Mehdi-KHALFALLAH/My-Arduino-UNO-Design/3D Component Models/3D_Model_ATMEGA16U2-AU.step

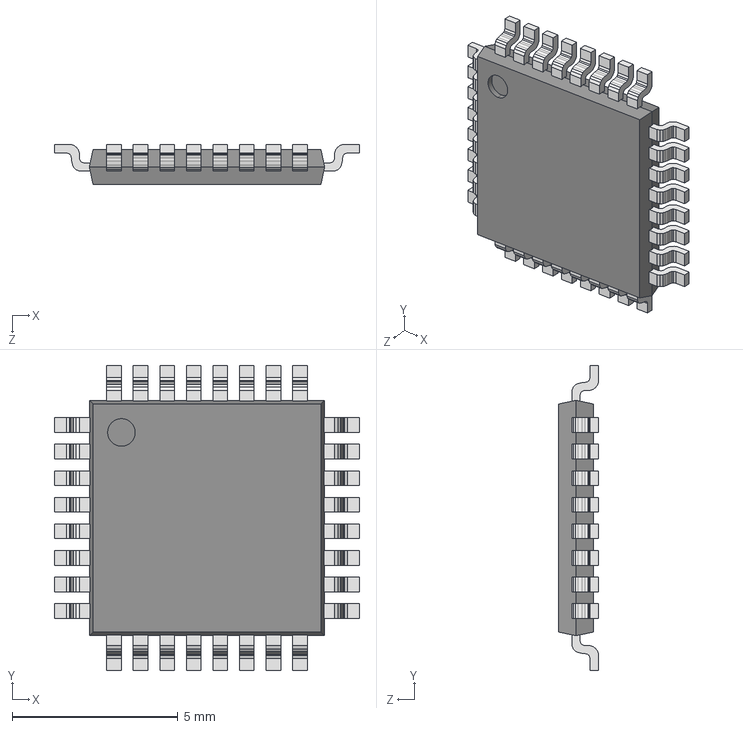
[picture p15: CAD file, 2020-09-16]
3D Component Models/3D_Model_ATMEGA16U2-AU.step
9.20 x 9.20 x 1.20 mm
