Mehdi-KHALFALLAH/My-Arduino-UNO-Design/3D Component Models/dil_socket.stp

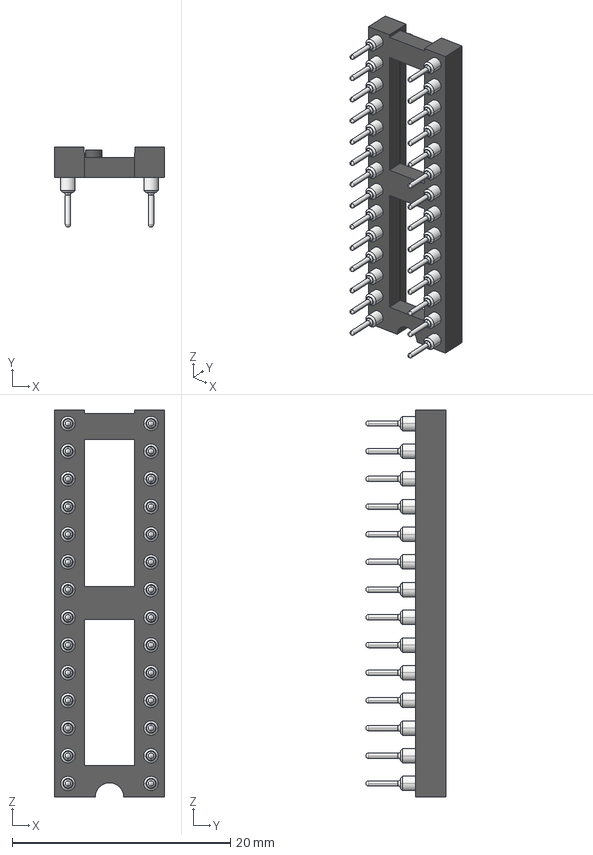
[picture p16: CAD file, 2020-09-16]
3D Component Models/dil_socket.stp
10.1 x 7.37 x 35.5 mm
