Mehdi-KHALFALLAH/My-Arduino-UNO-Design/3D Component Models/capacitor size C.step

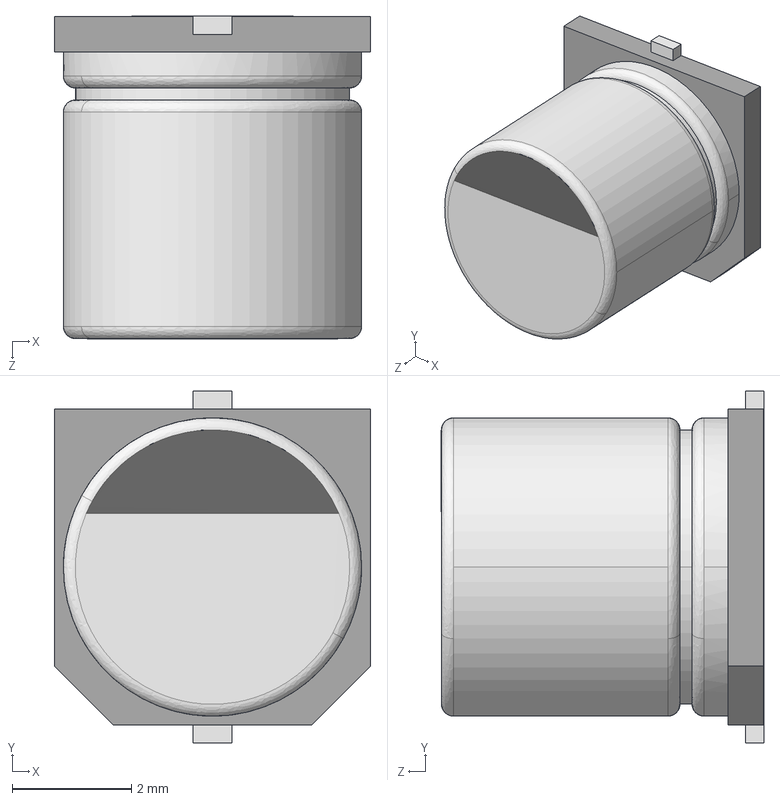
[picture p17: CAD file, 2020-09-16]
3D Component Models/capacitor size C.step
5.30 x 5.90 x 5.41 mm
