Mehdi-KHALFALLAH/My-Arduino-UNO-Design/3D Component Models/m20-7820842_asm.stp

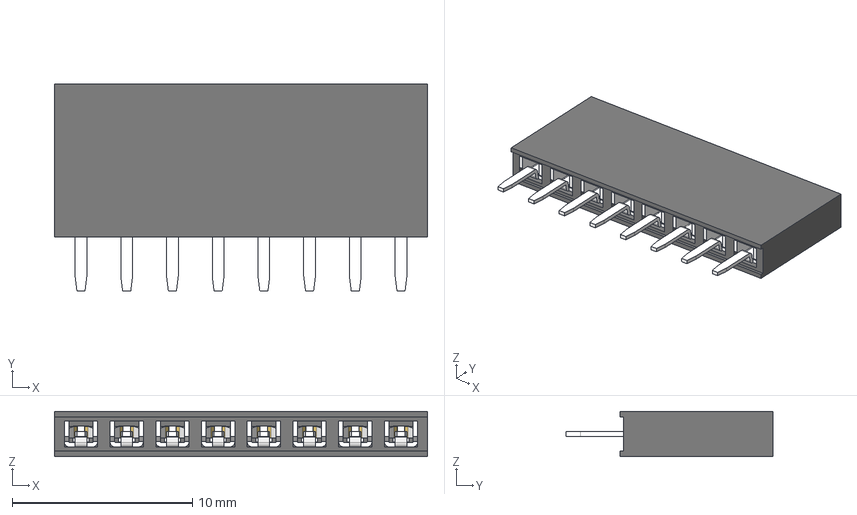
[picture p18: CAD file, 2020-09-16]
3D Component Models/m20-7820842_asm.stp
20.7 x 11.5 x 2.50 mm
M20-78208_MOULD
M20-782_CONTACT x 8
